LTVA1/STM32CrapSynth/STM32CrapSynthFirmware/src/external_flash.c

/*
 * external_flash.c
 *
 *  Created on: 12 ���. 2024 �.
 *      Author: georg
 */

#include "external_flash.h"
#include "spi.h"
#include "gpio.h"
#include "uart.h"
#include "stm32f3xx.h"
#include "main.h"

uint8_t spi_rx_double_buf[EXT_FLASH_RX_BUF_SIZE];
uint8_t spi_rx_buf[8];
uint8_t spi_tx_buf[EXT_FLASH_TX_BUF_SIZE];

extern uint8_t spi1_ready_tx;
extern uint8_t spi1_ready_rx;
extern Program_state_ccm state_ccm;

uint16_t manufacturer_id;
uint16_t device_id;
uint64_t device_uid;
uint32_t memory_size;

uint32_t erased_boundary;

uint8_t busy;

__attribute__((section (".ccmram")))
void external_flash_wait_until_not_busy()
{
	busy = 1;

	while(busy)
	{
		CS_EXT_FLASH_LOW

		//read status register 1
		//0x05, 8 bits of register
		spi_tx_buf[0] = 0x05;

		spi1_send_via_dma(&spi_tx_buf[0], 1);

		while(!spi1_ready_tx || !spi1_ready_rx) { asm("nop"); }
		while(!(SPI1->SR & SPI_SR_TXE) || (SPI1->SR & SPI_SR_BSY)) { asm("nop"); }

		spi1_receive_data_via_dma(&spi_rx_buf[0], 1);

		while(!spi1_ready_tx || !spi1_ready_rx) { asm("nop"); }
		while(!(SPI1->SR & SPI_SR_TXE) || (SPI1->SR & SPI_SR_BSY)) { asm("nop"); }

		if(!(spi_rx_buf[0] & 1))
		{
			busy = 0;
		}

		CS_EXT_FLASH_HIGH
	}
}

__attribute__((section (".ccmram")))
void external_flash_write_enable_command()
{
	//write enable
	//0x06
	spi_tx_buf[0] = 0x06;

	CS_EXT_FLASH_LOW
	spi1_send_via_dma(&spi_tx_buf[0], 1);

	while(!spi1_ready_tx || !spi1_ready_rx) { asm("nop"); }
	while(!(SPI1->SR & SPI_SR_TXE) || (SPI1->SR & SPI_SR_BSY)) { asm("nop"); }

	CS_EXT_FLASH_HIGH
}

__attribute__((section (".ccmram")))
void external_flash_erase_sector(uint32_t address)
{
	external_flash_write_enable_command();

	//sector erase (4KiB)
	//0x20, addr 24 bits (MSB to LSB)
	spi_tx_buf[0] = 0x20;
	spi_tx_buf[1] = (address >> 16) & 0xff;
	spi_tx_buf[2] = (address >> 8) & 0xff;
	spi_tx_buf[3] = address & 0xff;

	CS_EXT_FLASH_LOW
	spi1_send_via_dma(&spi_tx_buf[0], 4);

	while(!spi1_ready_tx || !spi1_ready_rx) { asm("nop"); }
	while(!(SPI1->SR & SPI_SR_TXE) || (SPI1->SR & SPI_SR_BSY)) { asm("nop"); }

	CS_EXT_FLASH_HIGH

	//poll status register until busy bit is reset
	external_flash_wait_until_not_busy();

	CS_EXT_FLASH_HIGH

	erased_boundary += 4 * 1024;
}

__attribute__((section (".ccmram")))
void external_flash_read_data(uint32_t address, uint8_t* data, uint16_t size, uint8_t start)
{
	while(!spi1_ready_tx || !spi1_ready_rx) { asm("nop"); }
	while(!(SPI1->SR & SPI_SR_TXE) || (SPI1->SR & SPI_SR_BSY)) { asm("nop"); }

	if(start) //we lower chip select and issue command only the 1st time
	// then we just read n bytes over and over without issuing a command
	{
		//read data
		//0x03, addr 24 bits (MSB to LSB)
		spi_tx_buf[0] = 0x03;
		spi_tx_buf[1] = (address >> 16) & 0xff;
		spi_tx_buf[2] = (address >> 8) & 0xff;
		spi_tx_buf[3] = address & 0xff;

		CS_EXT_FLASH_LOW
		spi1_send_via_dma(&spi_tx_buf[0], 4);

		while(!spi1_ready_tx || !spi1_ready_rx) { asm("nop"); }
		while(!(SPI1->SR & SPI_SR_TXE) || (SPI1->SR & SPI_SR_BSY)) { asm("nop"); }
	}

	spi1_receive_data_via_dma(data, size);
}

uint8_t test_data_read[256];

__attribute__((section (".ccmram")))
void external_flash_write_page(uint32_t address, uint8_t* data, uint16_t size)
{
	if(address == 0)
	{
		erased_boundary = 0; //we start writing from beginning
	}

	if(erased_boundary < address + (uint32_t)size)
	{
		external_flash_erase_sector(erased_boundary);
	}

	uint16_t curr_pos = 0;

	while(size > curr_pos)
	{
		external_flash_write_enable_command();

		//page program
		//0x02, addr 24 bits (MSB to LSB), up to 256 bytes of data
		spi_tx_buf[0] = 0x02;
		spi_tx_buf[1] = ((address + curr_pos) >> 16) & 0xff;
		spi_tx_buf[2] = ((address + curr_pos) >> 8) & 0xff;
		spi_tx_buf[3] = (address + curr_pos) & 0xff;

		CS_EXT_FLASH_LOW
		spi1_send_via_dma(&spi_tx_buf[0], 4);

		while(!spi1_ready_tx || !spi1_ready_rx) { asm("nop"); }
		while(!(SPI1->SR & SPI_SR_TXE) || (SPI1->SR & SPI_SR_BSY)) { asm("nop"); }

		spi1_send_via_dma(&data[curr_pos], ((size - curr_pos) > 256 ? 256 : (size - curr_pos)));

		while(!spi1_ready_tx || !spi1_ready_rx) { asm("nop"); }
		while(!(SPI1->SR & SPI_SR_TXE) || (SPI1->SR & SPI_SR_BSY)) { asm("nop"); }

		CS_EXT_FLASH_HIGH

		//poll status register until busy bit is reset
		external_flash_wait_until_not_busy();

		CS_EXT_FLASH_HIGH

		/*external_flash_read_data(address + curr_pos, test_data_read, size, 1);

		while(!spi1_ready_tx || !spi1_ready_rx) { asm("nop"); }
		while(!(SPI1->SR & SPI_SR_TXE) || (SPI1->SR & SPI_SR_BSY)) { asm("nop"); }

		CS_EXT_FLASH_HIGH

		for(int i = 0; i < ((size - curr_pos) > 256 ? 256 : (size - curr_pos)); i++)
		{
			if(test_data_read[i] != data[curr_pos + i])
			{
				asm("nop");
				int y = 0;
				asm("nop");
			}
		}*/

		curr_pos += 256;
	}
}

void external_flash_init_and_request_info()
{
	//we assume that the memory we are working with is either w25q80, w25q16, w25q32,   w25q64  or  w25q128
	//                                                  size:   1MiB    2MiB    4MiB     8MiB        16MiB
	//                                                    ID: 0x4014  0x4015  0x4016    0x6017      0x4018 OR 0x7018?
	//                                                                                 OR 0x4017?

	//reset
	spi_tx_buf[0] = 0x66;
	spi_tx_buf[1] = 0x99;

	CS_EXT_FLASH_LOW
	spi1_send_via_dma(&spi_tx_buf[0], 2);

	while(!spi1_ready_tx || !spi1_ready_rx) { asm("nop"); }
	while(!(SPI1->SR & SPI_SR_TXE) || (SPI1->SR & SPI_SR_BSY)) { asm("nop"); }

	CS_EXT_FLASH_HIGH

	//100 ms delay
	for(int i = 0; i < 320000; i++) { asm("nop"); }

	CS_EXT_FLASH_LOW
	//request manufacturer/device ID
	//0x9f, manufacturer ID, device ID MSB, device ID LSB
	spi_tx_buf[0] = 0x9f;

	spi1_send_via_dma(&spi_tx_buf[0], 1);

	while(!spi1_ready_tx || !spi1_ready_rx) { asm("nop"); }
	while(!(SPI1->SR & SPI_SR_TXE) || (SPI1->SR & SPI_SR_BSY)) { asm("nop"); }

	spi1_receive_data_via_dma(&spi_rx_buf[0], 3);

	while(!spi1_ready_tx || !spi1_ready_rx) { asm("nop"); }
	while(!(SPI1->SR & SPI_SR_TXE) || (SPI1->SR & SPI_SR_BSY)) { asm("nop"); }

	CS_EXT_FLASH_HIGH

	manufacturer_id = spi_rx_buf[0];
	device_id = (spi_rx_buf[1] << 8) | spi_rx_buf[2];

	if(device_id == 0x4014) memory_size = 1024 * 1024;
	if(device_id == 0x4015) memory_size = 1024 * 1024 * 2;
	if(device_id == 0x4016) memory_size = 1024 * 1024 * 4;
	if(device_id == 0x4017 || device_id == 0x6017) memory_size = 1024 * 1024 * 8;
	if(device_id == 0x4018 || device_id == 0x7018) memory_size = 1024 * 1024 * 16;

	//device unique ID
	//0x4B, dummy, dummy, dummy, dummy, UID MSB to LSB (8 bytes)
	spi_tx_buf[0] = 0x4B;
	spi_tx_buf[1] = 0; //just in case
	spi_tx_buf[2] = 0;
	spi_tx_buf[3] = 0;
	spi_tx_buf[4] = 0;

	CS_EXT_FLASH_LOW

	spi1_send_via_dma(&spi_tx_buf[0], 5);

	while(!spi1_ready_tx || !spi1_ready_rx) { asm("nop"); }
	while(!(SPI1->SR & SPI_SR_TXE) || (SPI1->SR & SPI_SR_BSY)) { asm("nop"); }

	spi1_receive_data_via_dma(&spi_rx_buf[0], 8);

	while(!spi1_ready_tx || !spi1_ready_rx) { asm("nop"); }
	while(!(SPI1->SR & SPI_SR_TXE) || (SPI1->SR & SPI_SR_BSY)) { asm("nop"); }

	CS_EXT_FLASH_HIGH

	device_uid =
		((uint64_t)spi_rx_buf[0] << 56) |
		((uint64_t)spi_rx_buf[1] << 48) |
		((uint64_t)spi_rx_buf[2] << 40) |
		((uint64_t)spi_rx_buf[3] << 32) |
		((uint64_t)spi_rx_buf[4] << 24) |
		((uint64_t)spi_rx_buf[5] << 16) |
		((uint64_t)spi_rx_buf[6] << 8) |
		(uint64_t)spi_rx_buf[7];

	erased_boundary = 0;
}

__attribute__((section (".ccmram")))
void external_flash_write_page_task()
{
	if(state_ccm.state != STATE_PROG_EXTERNAL_FLASH) return;

	external_flash_write_page(state_ccm.block_start_offset, state_ccm.data_pointer, state_ccm.block_length);

	uart_send_response();

	state_ccm.state = STATE_IDLE;
}
