LTVA1/STM32CrapSynth/STM32CrapSynthFirmware/src/ad9833.c

/*
 * ad9833.c
 *
 *  Created on: 16 ���. 2024 �.
 *      Author: Georg
 */

#include "ad9833.h"
#include "stm32f3xx.h"
#include "spi.h"
#include "gpio.h"

extern uint8_t spi2_ready;

uint16_t spi_tx_buf_ad9833[AD9833_NUM][AD9833_TX_BUF_SIZE];
uint8_t waves[4] = { WAVE_SINE, WAVE_TRIANGLE, WAVE_SQUARE, WAVE_SQUARE_DOUBLE_FREQ };

uint8_t dds_freq_reg[4];

__attribute__((section (".ccmram")))
void ad9833_cs_low(uint8_t dds)
{
	switch(dds)
	{
		case 0:
		{
			CS_AD1_LOW
			break;
		}
		case 1:
		{
			CS_AD2_LOW
			break;
		}
		case 2:
		{
			CS_AD3_LOW
			break;
		}
		case 3:
		{
			CS_AD4_LOW
			break;
		}
		default: break;
	}
}

__attribute__((section (".ccmram")))
void ad9833_cs_high(uint8_t dds)
{
	switch(dds)
	{
		case 0:
		{
			CS_AD1_HIGH
			break;
		}
		case 1:
		{
			CS_AD2_HIGH
			break;
		}
		case 2:
		{
			CS_AD3_HIGH
			break;
		}
		case 3:
		{
			CS_AD4_HIGH
			break;
		}
		default: break;
	}
}

__attribute__((section (".ccmram")))
void ad9833_reset(uint8_t dds)
{
	spi_tx_buf_ad9833[dds][0] |= RESET_BIT; //reset bit on

	ad9833_cs_low(dds);
	spi2_send_16bits(spi_tx_buf_ad9833[dds][0]);
	ad9833_cs_high(dds);

	spi_tx_buf_ad9833[dds][0] &= ~RESET_BIT; //reset bit off

	ad9833_cs_low(dds);
	spi2_send_16bits(spi_tx_buf_ad9833[dds][0]); //exit reset, as in application note 1070
	ad9833_cs_high(dds);
}

__attribute__((section (".ccmram")))
void ad9833_write_freq(uint8_t dds, uint32_t freq)
{
	spi_tx_buf_ad9833[dds][1] = (dds_freq_reg[dds] ? FREQ1_REG_ADDRESS : FREQ0_REG_ADDRESS) | (freq & 0x3fff);
	spi_tx_buf_ad9833[dds][2] = (dds_freq_reg[dds] ? FREQ1_REG_ADDRESS : FREQ0_REG_ADDRESS) | ((freq >> 14) & 0x3fff);

	ad9833_cs_low(dds);
	spi2_send_16bits(spi_tx_buf_ad9833[dds][1]);
	spi2_send_16bits(spi_tx_buf_ad9833[dds][2]);
	ad9833_cs_high(dds);

	spi_tx_buf_ad9833[dds][0] &= ~FSELECT;

	if(dds_freq_reg[dds])
	{
		spi_tx_buf_ad9833[dds][0] |= FSELECT;
	}

	ad9833_cs_low(dds);
	spi2_send_16bits(spi_tx_buf_ad9833[dds][0]);
	ad9833_cs_high(dds);

	dds_freq_reg[dds]++;
	dds_freq_reg[dds] &= 1;
}

__attribute__((section (".ccmram")))
void ad9833_change_wave(uint8_t dds, uint8_t wave)
{
	spi_tx_buf_ad9833[dds][0] &= ~(WAVE_MASK);
	spi_tx_buf_ad9833[dds][0] |= waves[wave];

	ad9833_cs_low(dds);
	spi2_send_16bits(spi_tx_buf_ad9833[dds][0]);
	ad9833_cs_high(dds);
}

void ad9833_init(uint8_t dds)
{
	spi_tx_buf_ad9833[dds][0] |= B28;
	ad9833_reset(dds);
	dds_freq_reg[dds] = 0;
	ad9833_write_freq(dds, 0);
}

void ad9833_init_all()
{
	for(int i = 0; i < AD9833_NUM; i++)
	{
		ad9833_init(i);
	}
}
