LTVA1/STM32CrapSynth/STM32CrapSynthFirmware/src/ad9833.h

/*
 * ad9833.h
 *
 *  Created on: 16 ���. 2024 �.
 *      Author: Georg
 */

#ifndef AD9833_H_
#define AD9833_H_

#include <stdint.h>

#define AD9833_TX_BUF_SIZE 3
#define AD9833_NUM 4

#define FREQ0_REG_ADDRESS (0b01 << 14)
#define FREQ1_REG_ADDRESS (0b10 << 14)

#define RESET_BIT (1 << 8)
#define B28 (1 << 13) /* two 14-bit writes, update of internal reg after 2nd write */
#define FSELECT (1 << 11)
#define WAVE_MASK ((1 << 5) | (1 << 3) | (1 << 1))
#define WAVE_SQUARE (1 << 5)
#define WAVE_SQUARE_DOUBLE_FREQ ((1 << 5) | (1 << 3))
#define WAVE_SINE 0
#define WAVE_TRIANGLE (1 << 1)

void ad9833_reset(uint8_t dds);
void ad9833_write_freq(uint8_t dds, uint32_t freq);
void ad9833_change_wave(uint8_t dds, uint8_t wave);
void ad9833_init(uint8_t dds);
void ad9833_init_all();

#endif /* AD9833_H_ */
